vuquangtrong/esp32s3-gnss-base-station/docs/esp32-s3/ESP32S3WROOM1U.webp

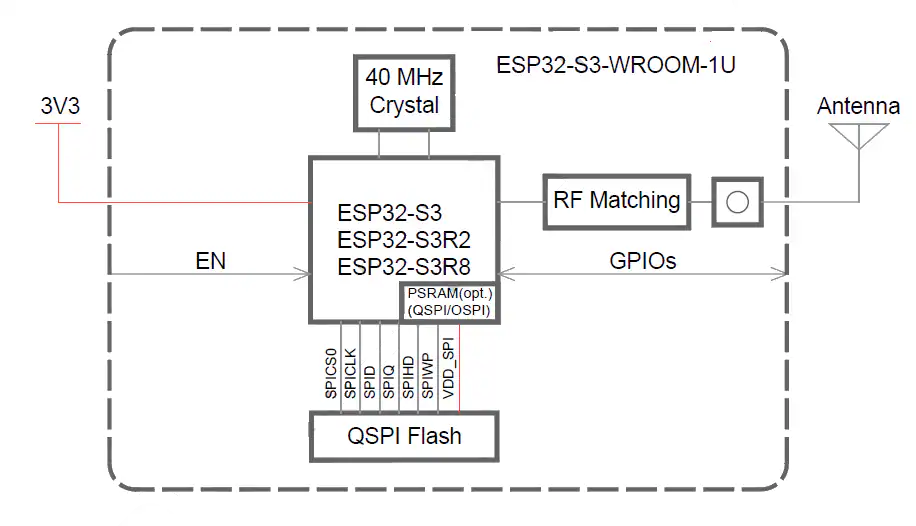
docs/esp32-s3/ESP32S3WROOM1U.webp
