vuquangtrong/esp32s3-gnss-base-station/hardware/order/Screenshot 2025-12-17 at 14-31-57 BOM and CPL Ipload - JLCPCB.png

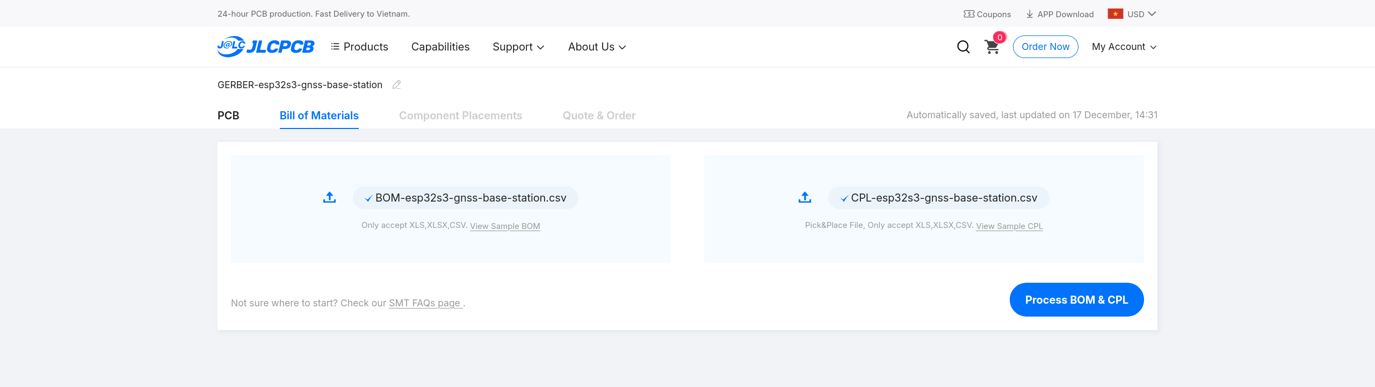
hardware/order/Screenshot 2025-12-17 at 14-31-57 BOM and CPL Ipload - JLCPCB.png
