vuquangtrong/esp32s3-gnss-base-station/hardware/order/Screenshot 2025-12-17 at 14-32-40 CPL Preview - JLCPCB.png

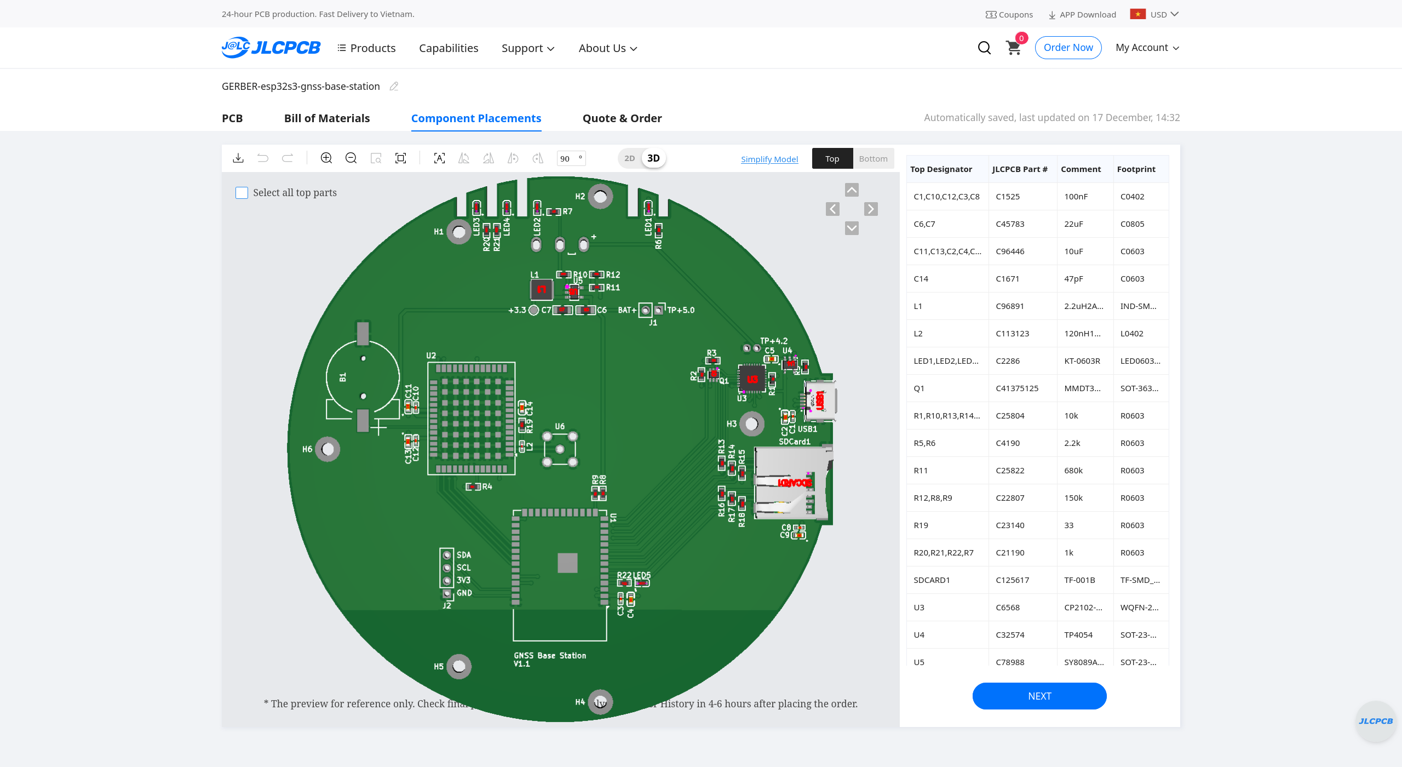
hardware/order/Screenshot 2025-12-17 at 14-32-40 CPL Preview - JLCPCB.png
