vuquangtrong/esp32s3-gnss-base-station/hardware/order/Screenshot 2025-12-17 at 14-34-29 CPL Preview - JLCPCB.jpeg

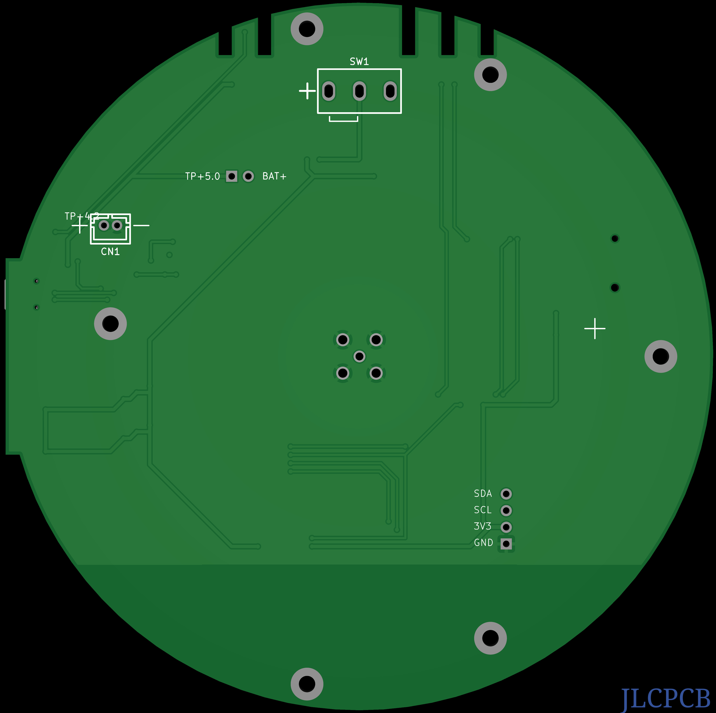
hardware/order/Screenshot 2025-12-17 at 14-34-29 CPL Preview - JLCPCB.jpeg
