vuquangtrong/esp32s3-gnss-base-station/firmware/main/wifi.h

#ifndef WIFI_H
#define WIFI_H

#include "esp_err.h"
#include "esp_netif.h"

#define WIFI_AP_SSID_PREFIX     "GNSS_"
#define WIFI_AP_PASSWORD        "12345678"
#define WIFI_STA_RETRY_MAX      10
#define WIFI_DISCONNECTED_BIT   BIT0
#define WIFI_DISCONNECT_TIMEOUT 10000

esp_err_t wifi_init(void);
esp_netif_t* wifi_get_ap_netif(void);
esp_netif_t* wifi_get_sta_netif(void);
esp_err_t wifi_sta_connect(const char* ssid, const char* password);

#endif  // WIFI_H
